Akshay6766/Guiding_Waves_Full-Code/20230930_004818.jpg

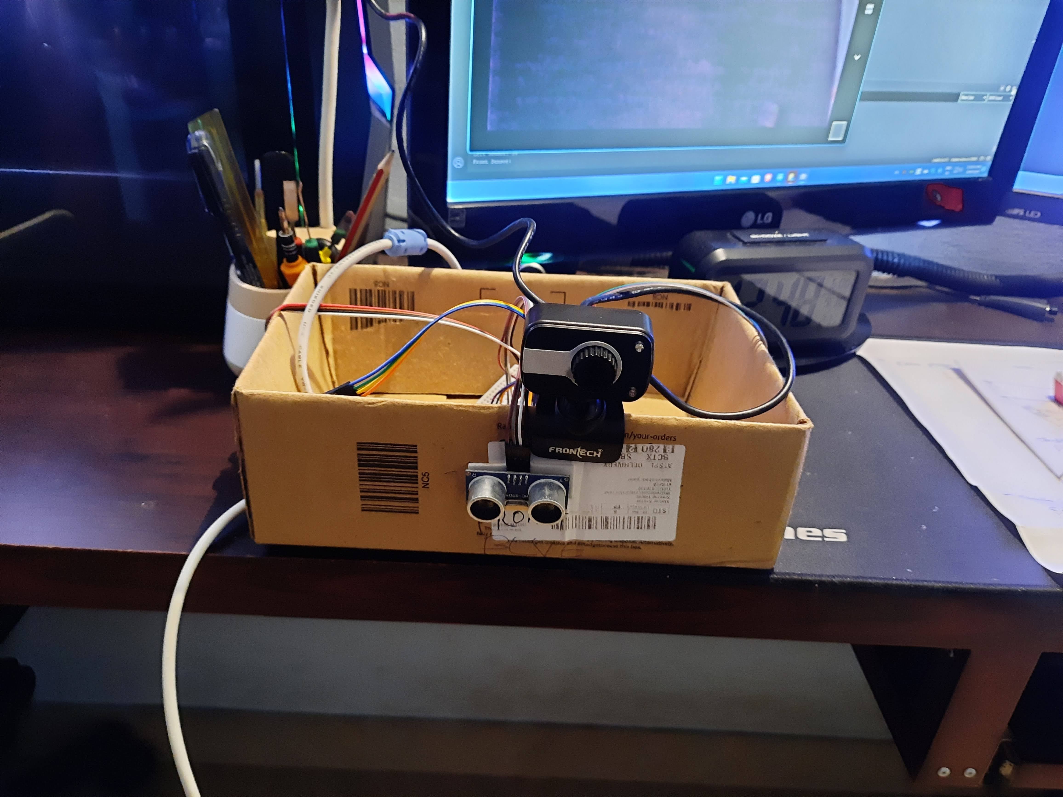
20230930_004818.jpg
