Akshay6766/Guiding_Waves_Full-Code/20230930_004853.jpg

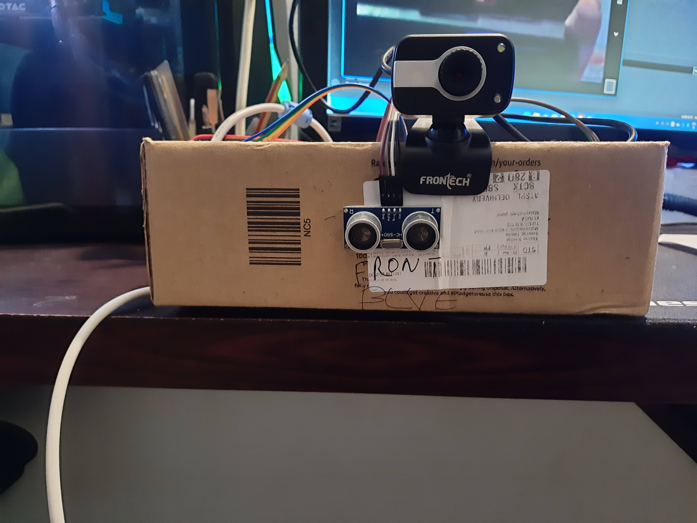
20230930_004853.jpg
