Akshay6766/Guiding_Waves_Full-Code/20231125_180546.jpg

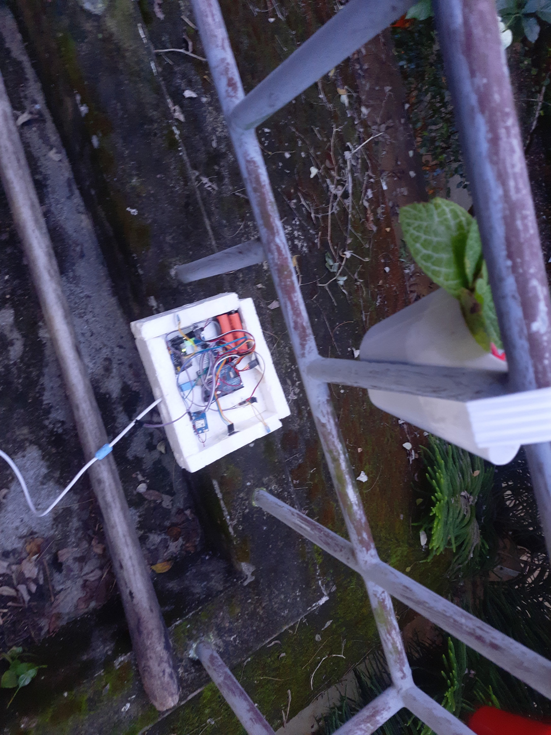
20231125_180546.jpg
