Akshay6766/Guiding_Waves_Full-Code/20231130_224902.jpg

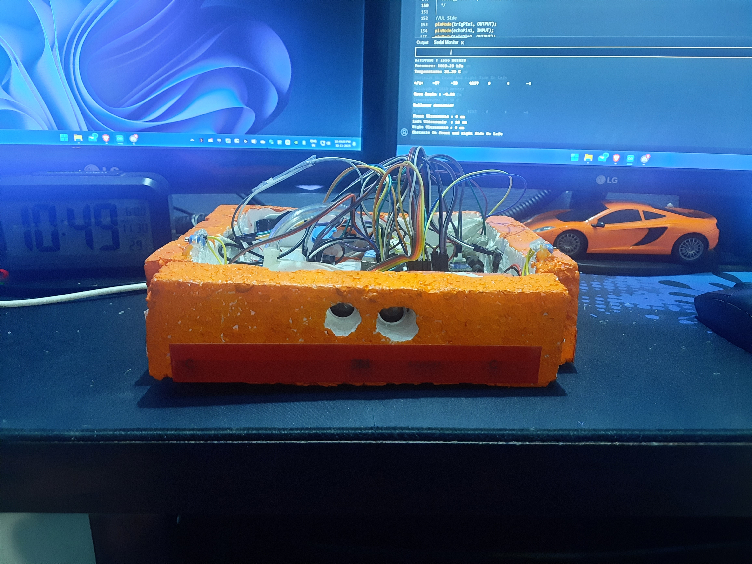
20231130_224902.jpg
