Akshay6766/Guiding_Waves_Full-Code/20231130_225711.jpg

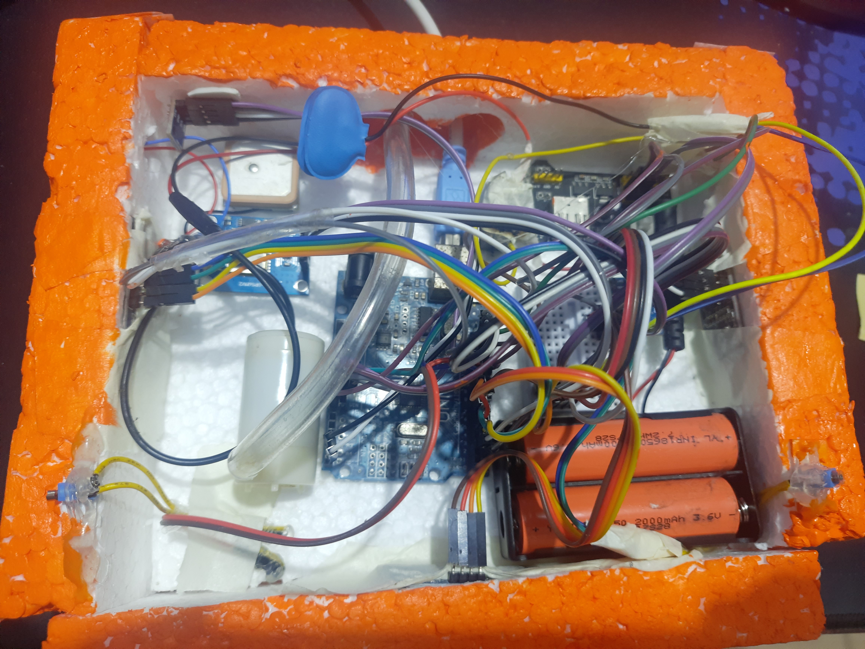
20231130_225711.jpg
