Akshay6766/Guiding_Waves_Full-Code/20231130_234025.jpg

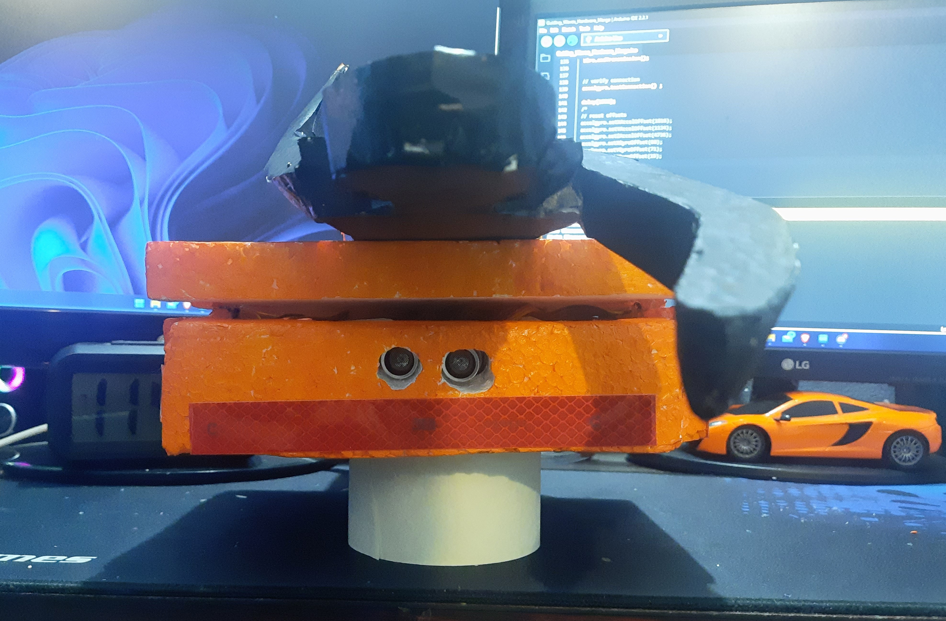
20231130_234025.jpg
